aindustriosa/AIndustriosa-Branding/5-PCBs/Master-ESP32/CNC/Master-ESP32C-agujero.png

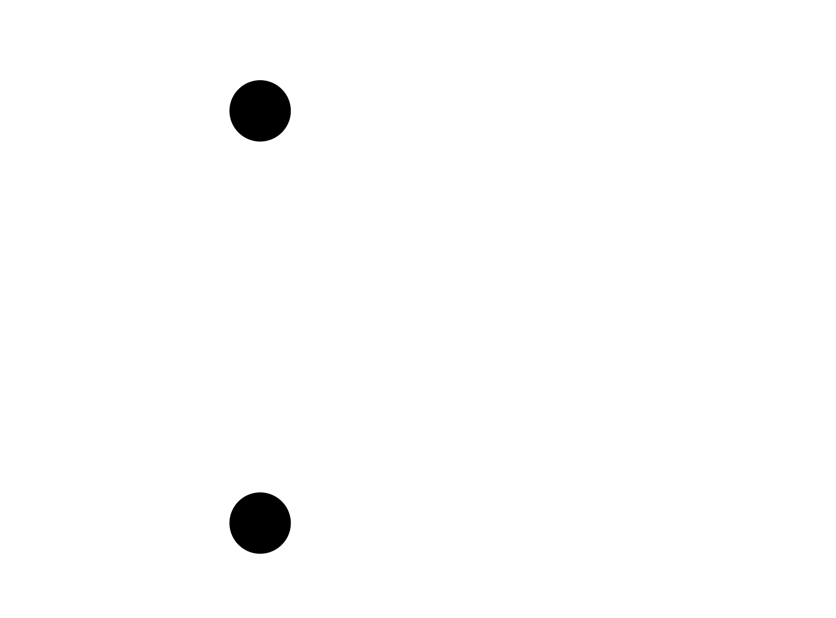
5-PCBs/Master-ESP32/CNC/Master-ESP32C-agujero.png
