aindustriosa/AIndustriosa-Branding/5-PCBs/Master-ESP32/CNC/Master-ESP32C-pistas.png

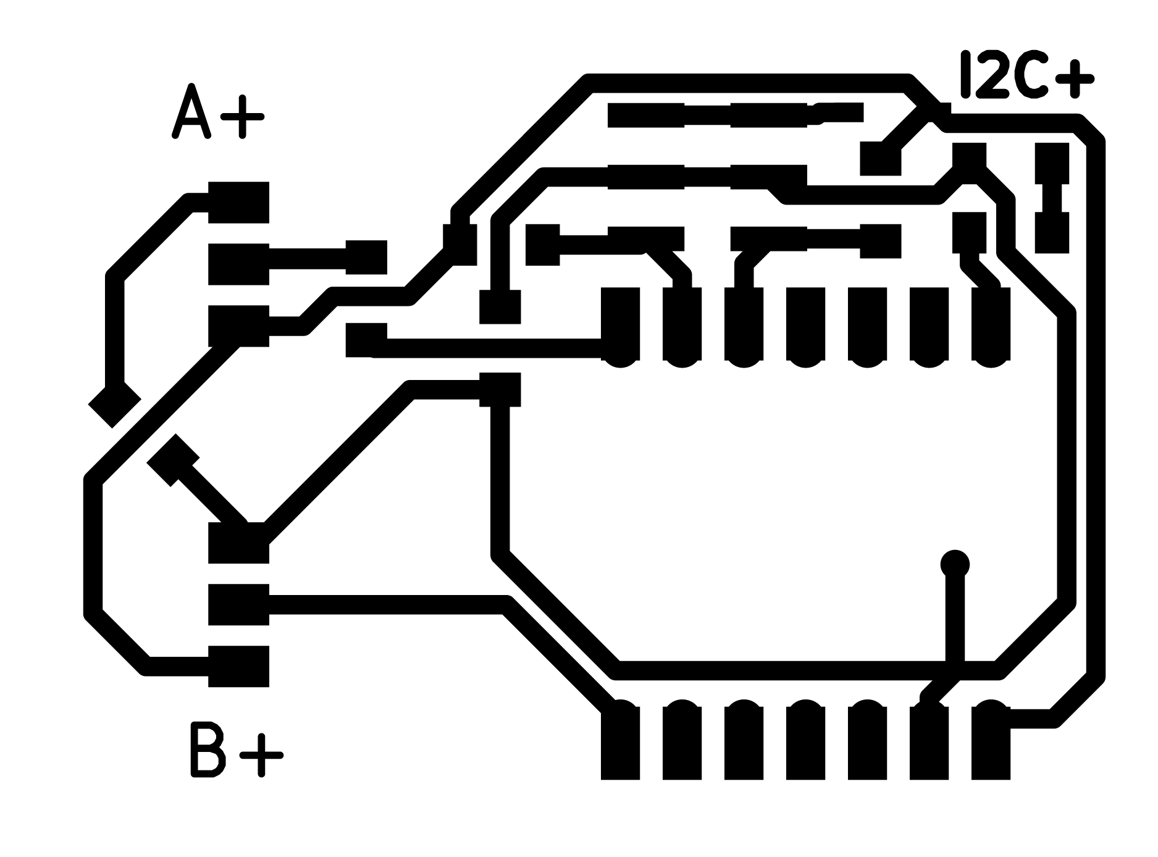
5-PCBs/Master-ESP32/CNC/Master-ESP32C-pistas.png
