aindustriosa/AIndustriosa-Branding/5-PCBs/Node-412/CNCx4b/Node-412B_corte.png

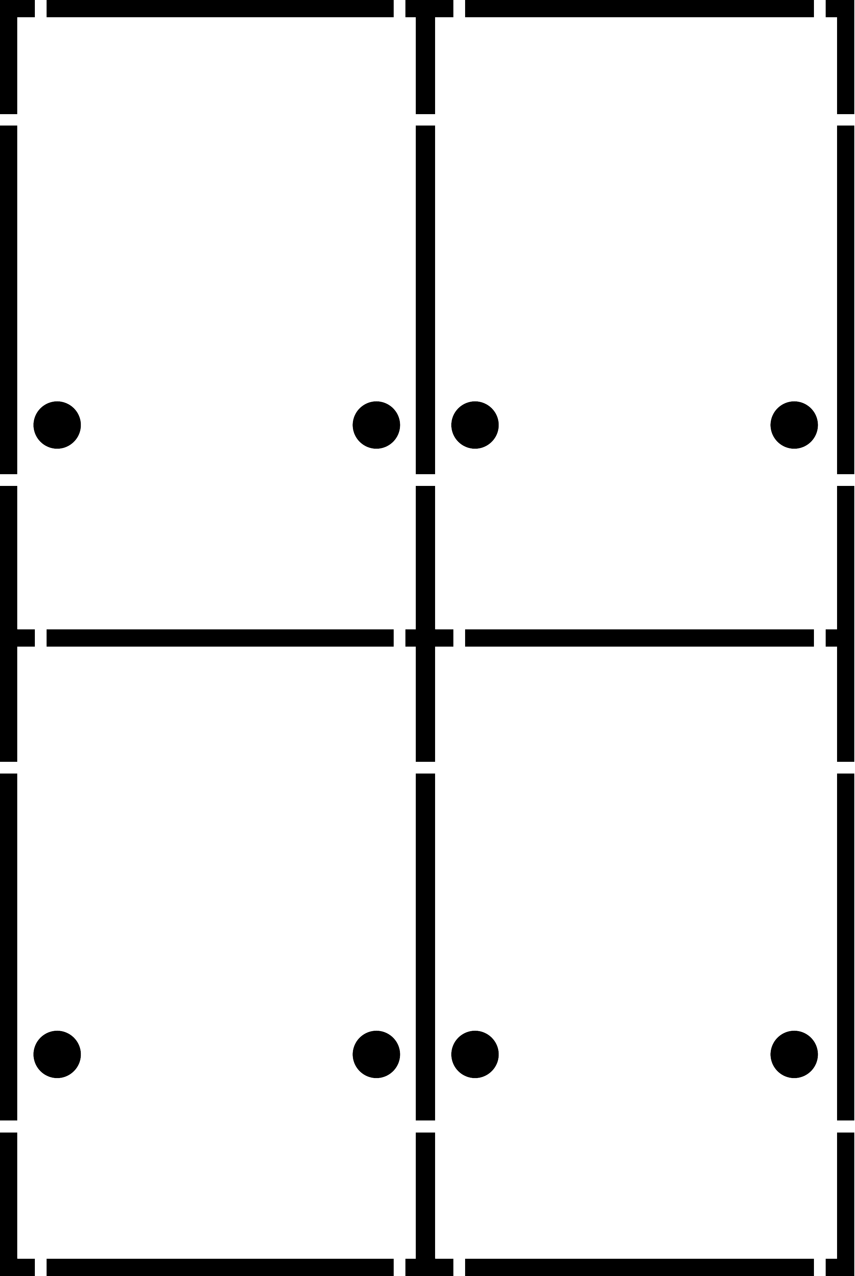
5-PCBs/Node-412/CNCx4b/Node-412B_corte.png
