aindustriosa/AIndustriosa-Branding/images/PI1.jpg

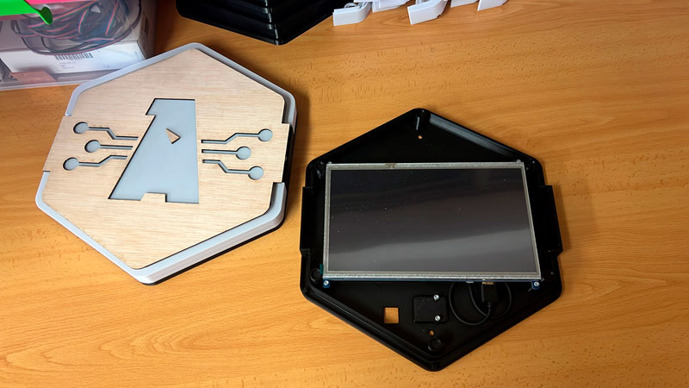
images/PI1.jpg
